scorninpc/filamentextruderboard/board/photos/01.jpeg

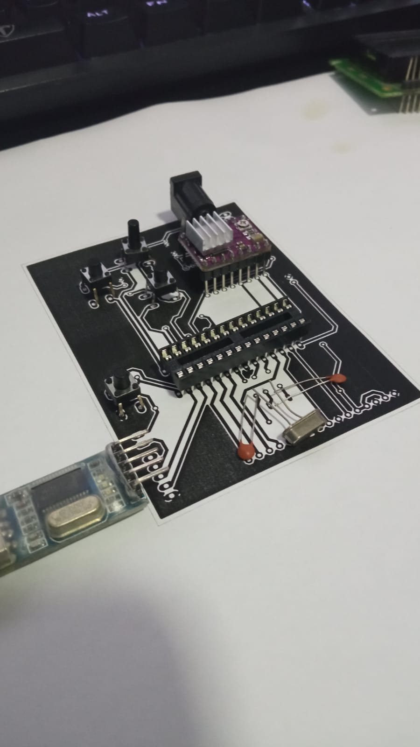
board/photos/01.jpeg
