scorninpc/filamentextruderboard/board/photos/04.jpeg

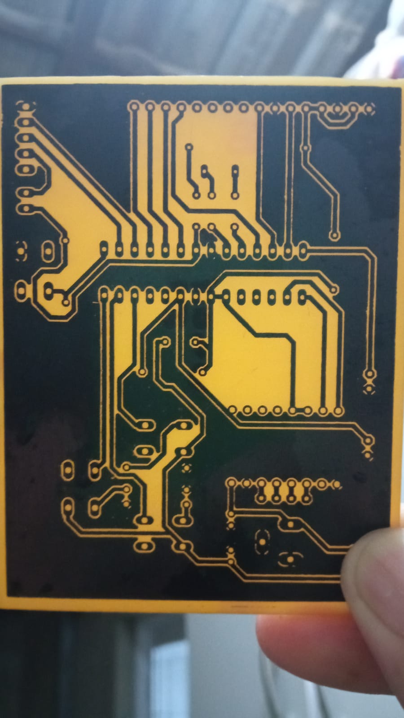
board/photos/04.jpeg
