scorninpc/filamentextruderboard/board/photos/05.jpeg

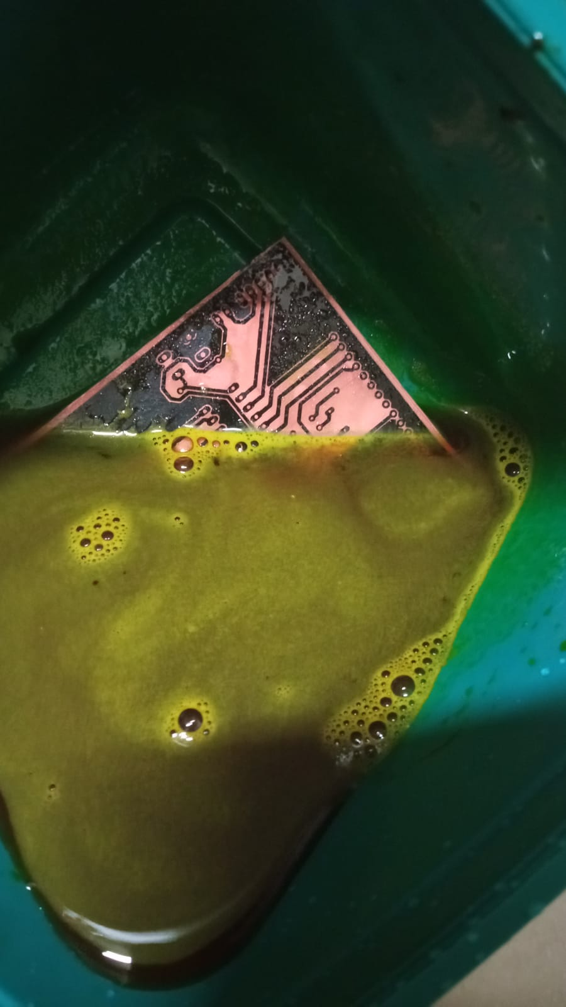
board/photos/05.jpeg
