scorninpc/filamentextruderboard/board/photos/06.jpeg

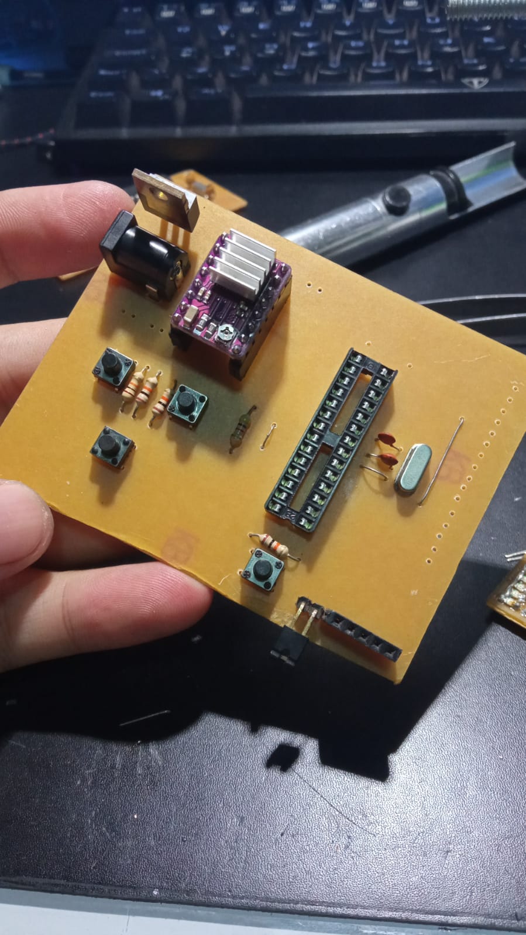
board/photos/06.jpeg
