scorninpc/filamentextruderboard/board/photos/07.jpeg

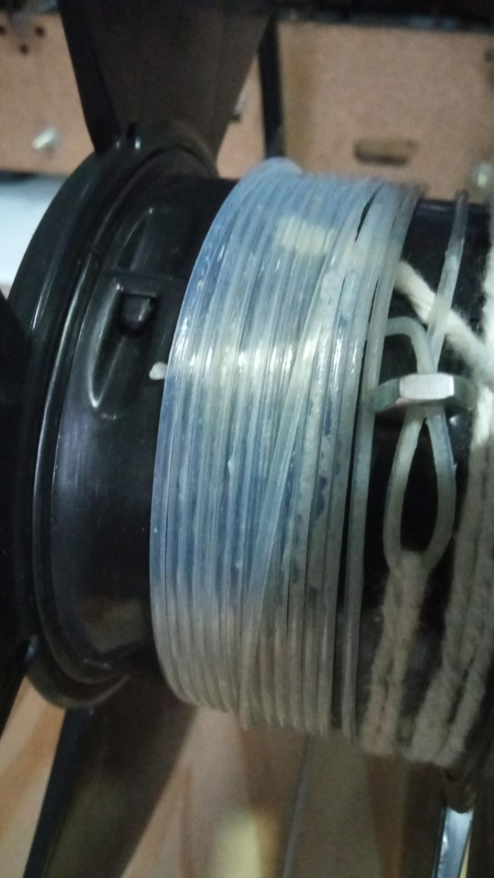
board/photos/07.jpeg
