scorninpc/filamentextruderboard/references/2021-10-12_18-17.png

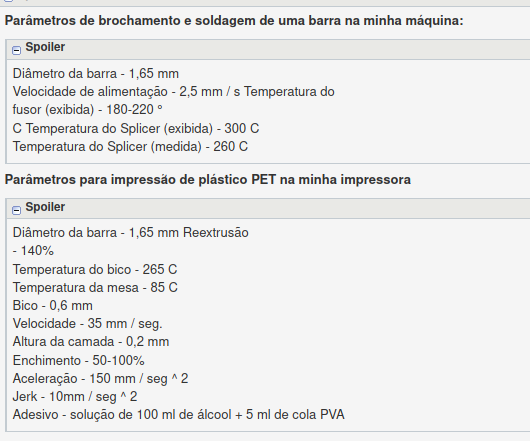
references/2021-10-12_18-17.png
